JPhilC/LunaticAstro.Diy.FilterWheel/Hardware/20260319_092125.JPG

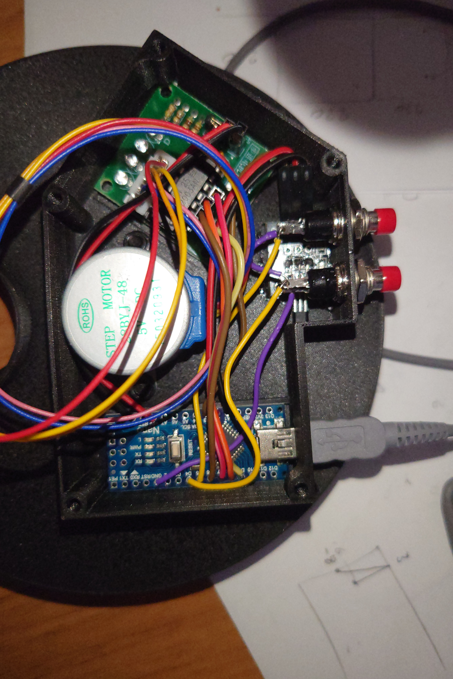
Hardware/20260319_092125.JPG
