JPhilC/LunaticAstro.Diy.FilterWheel/Hardware/20260319_092506.JPG

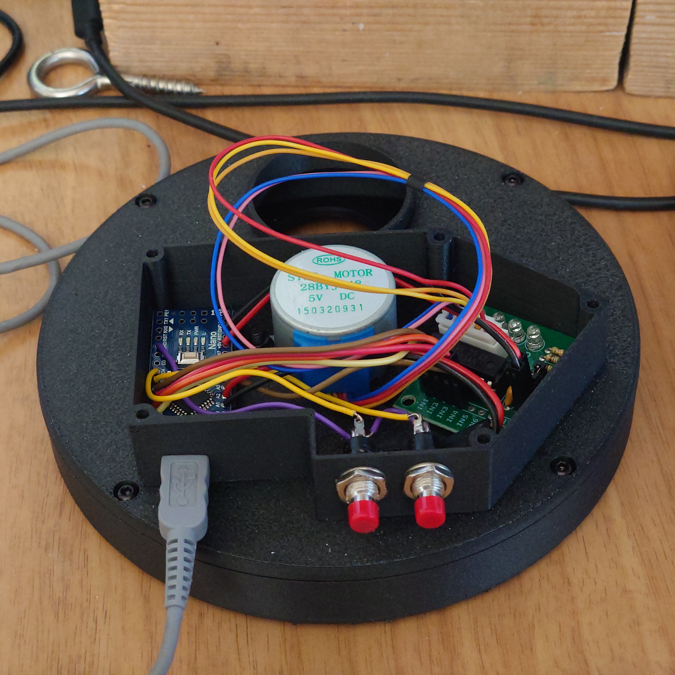
Hardware/20260319_092506.JPG
